BoomerChiao/ArduinoBirthday-Gift-DIY/JPG/3D_STL.jpg

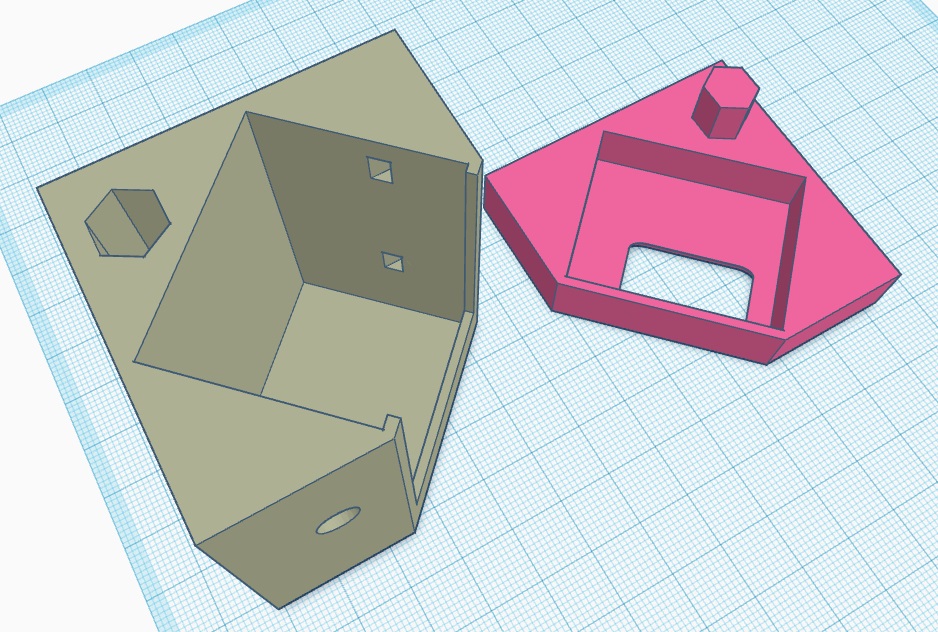
JPG/3D_STL.jpg
