BoomerChiao/ArduinoBirthday-Gift-DIY/JPG/3D_STL_V1.jpg

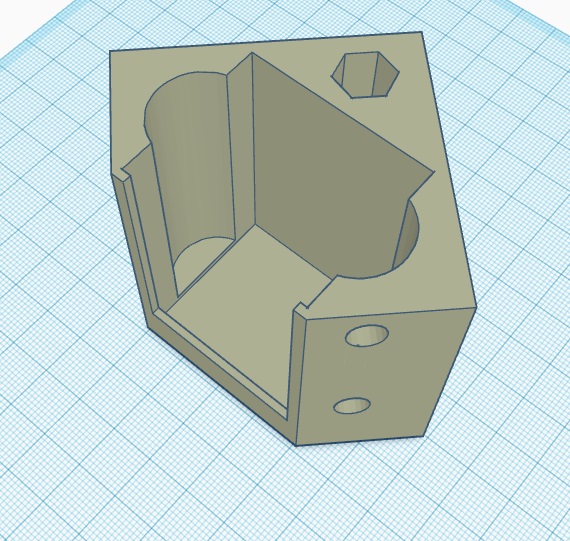
JPG/3D_STL_V1.jpg
