BoomerChiao/ArduinoBirthday-Gift-DIY/JPG/Arduino_pro_mini_LINE.png

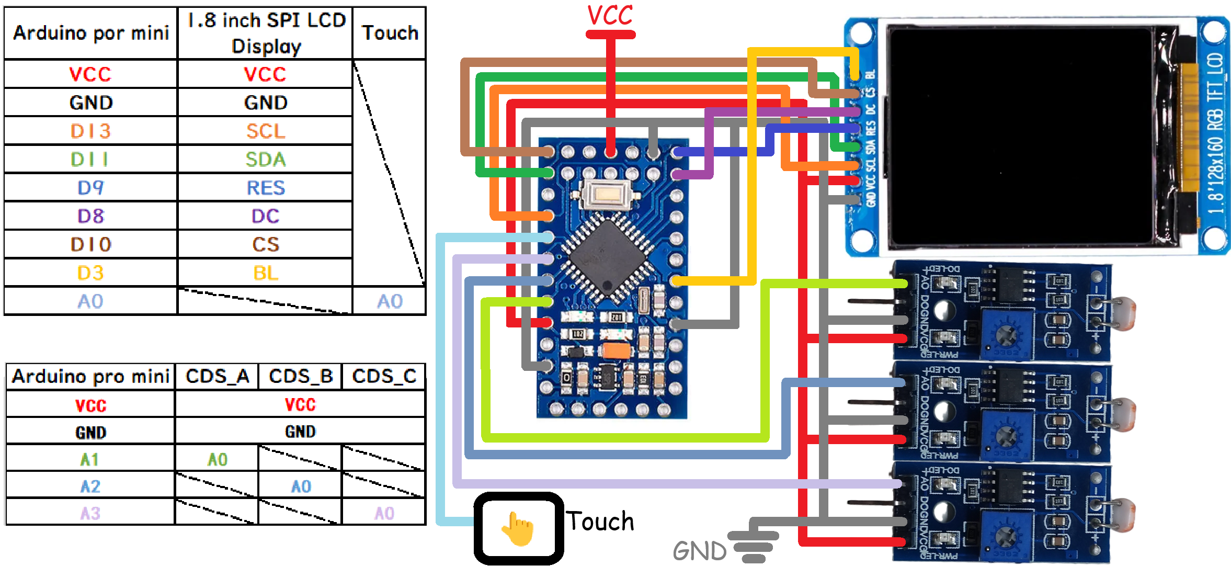
JPG/Arduino_pro_mini_LINE.png
