BoomerChiao/ArduinoBirthday-Gift-DIY/JPG/code.jpg

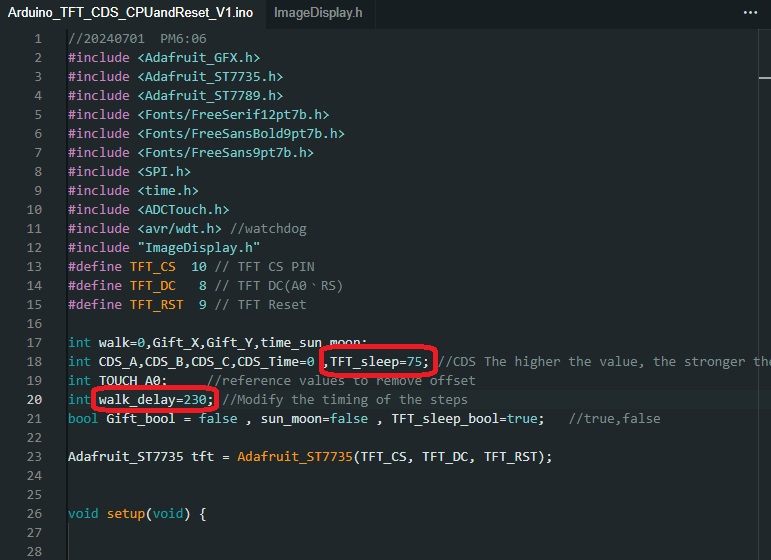
JPG/code.jpg
