BoomerChiao/ArduinoBirthday-Gift-DIY/JPG/IMG_7127.JPG

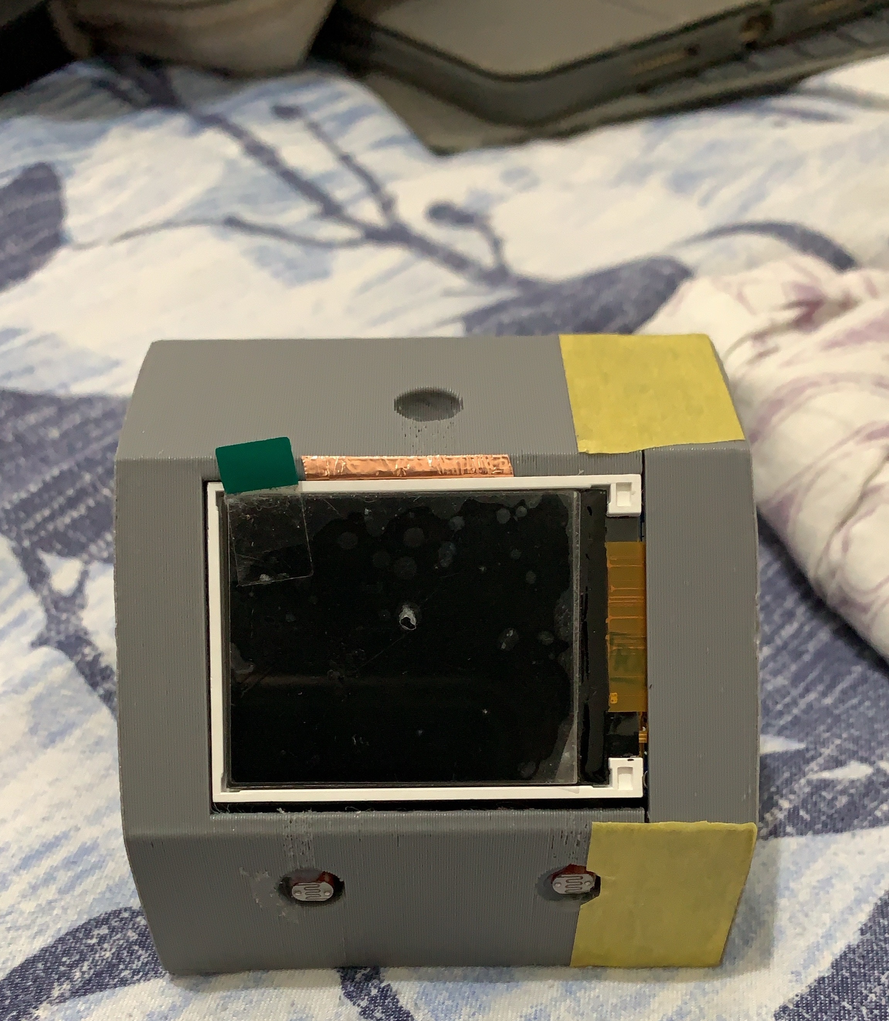
JPG/IMG_7127.JPG
