BoomerChiao/ArduinoBirthday-Gift-DIY/JPG/IMG_7605.jpg

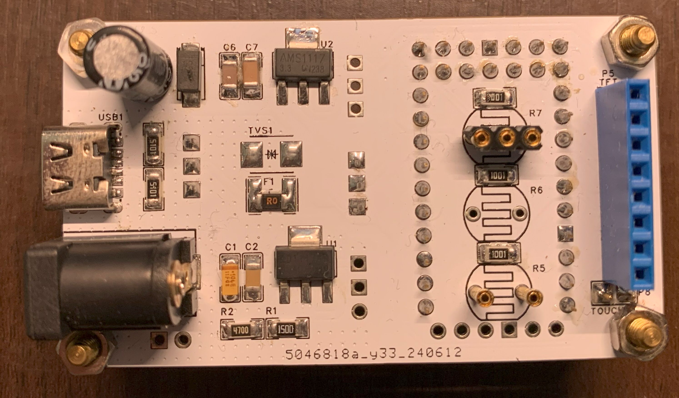
JPG/IMG_7605.jpg
