BoomerChiao/ArduinoBirthday-Gift-DIY/JPG/IMG_7606.jpg

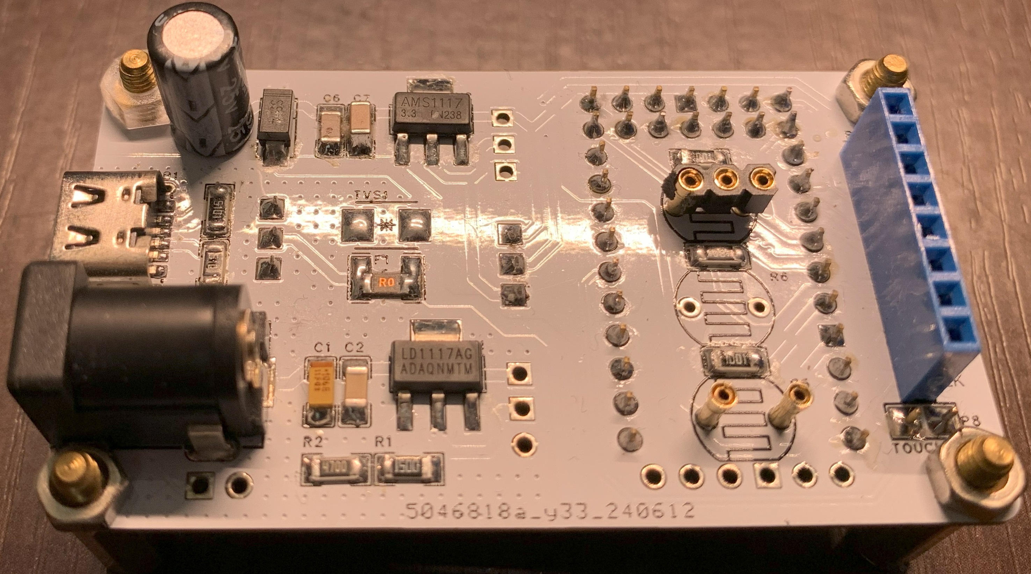
JPG/IMG_7606.jpg
