BoomerChiao/ArduinoBirthday-Gift-DIY/JPG/IMG_7607.jpg

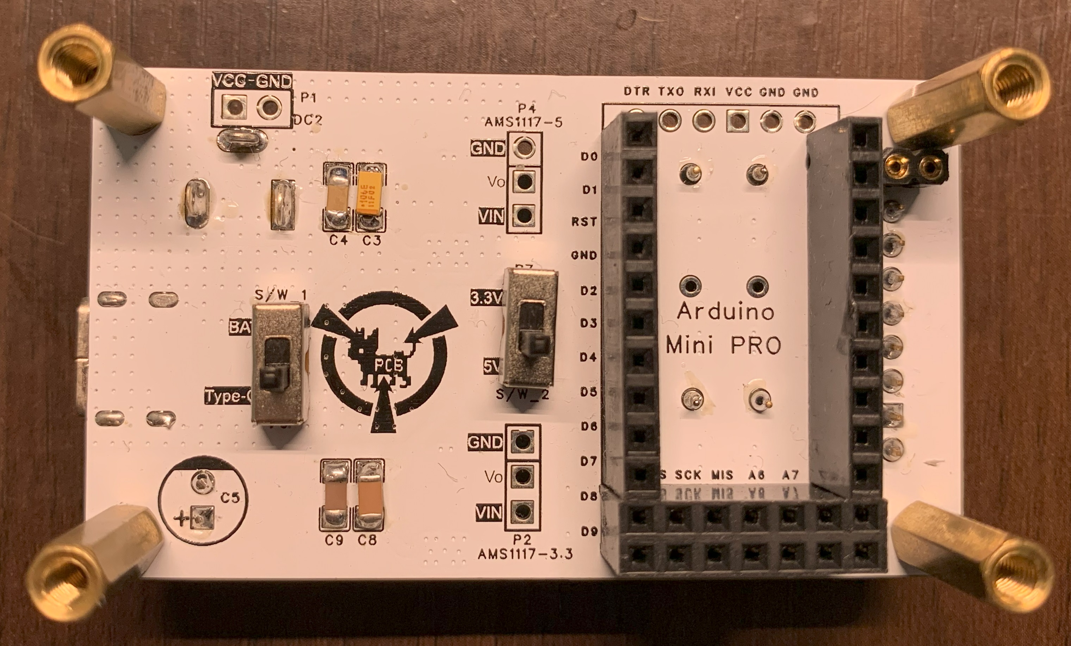
JPG/IMG_7607.jpg
