BoomerChiao/ArduinoBirthday-Gift-DIY/JPG/IMG_7608.jpg

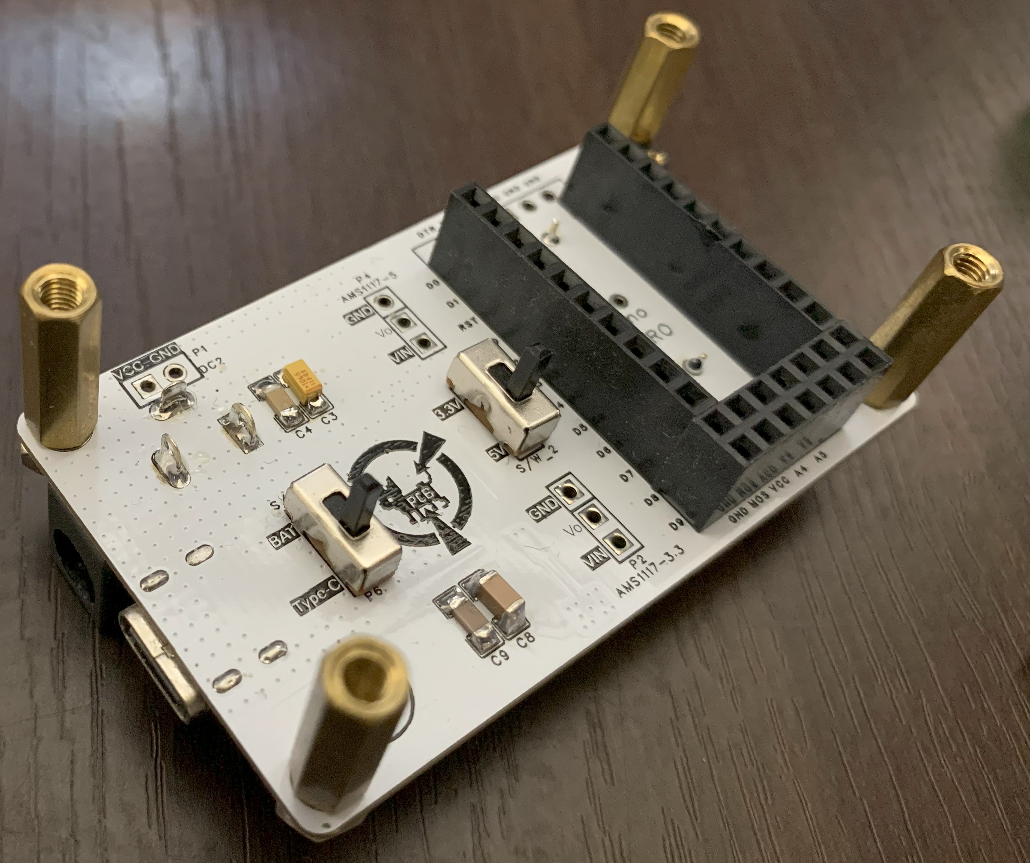
JPG/IMG_7608.jpg
