BoomerChiao/ArduinoBirthday-Gift-DIY/JPG/IMG_7611.jpg

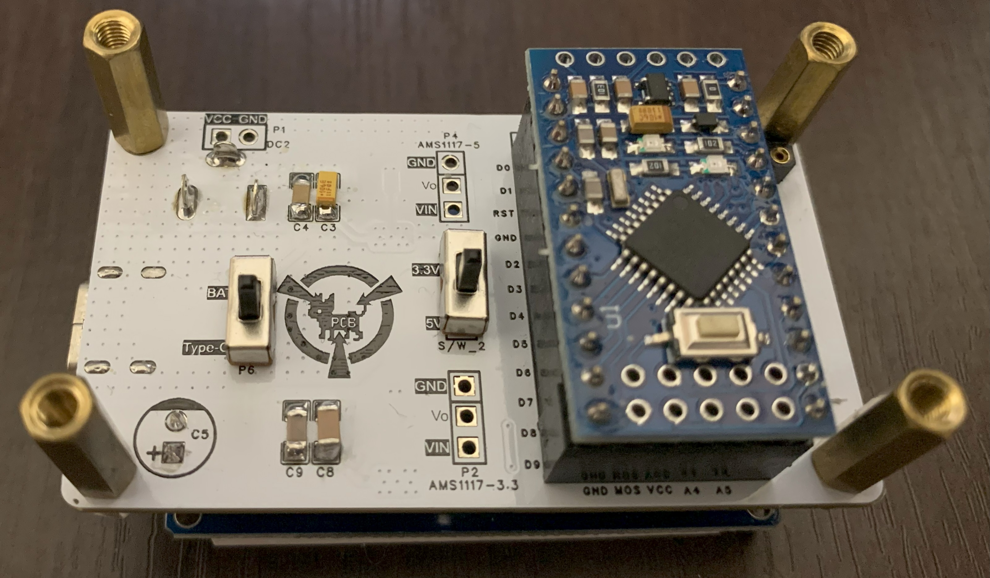
JPG/IMG_7611.jpg
