BoomerChiao/ArduinoBirthday-Gift-DIY/JPG/IMG_7613.jpg

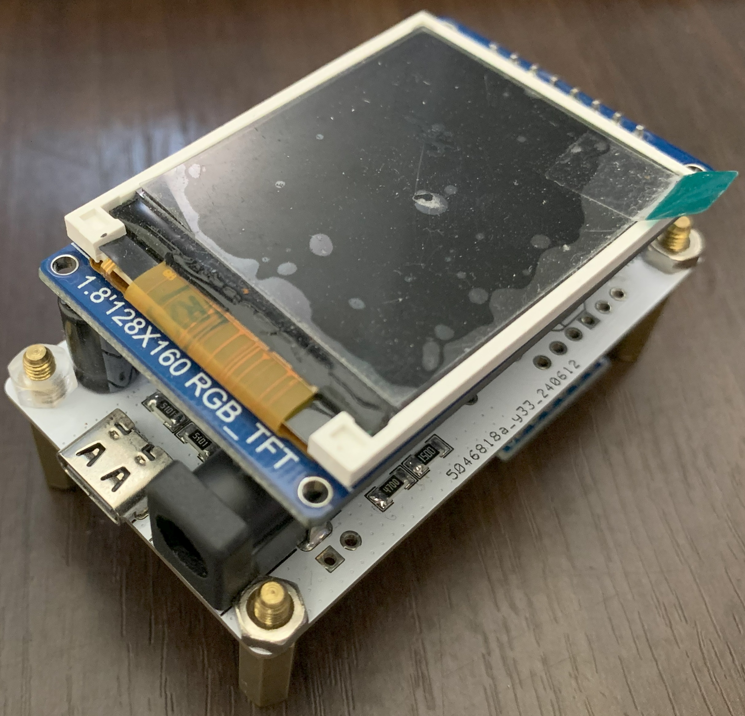
JPG/IMG_7613.jpg
