BoomerChiao/ArduinoBirthday-Gift-DIY/JPG/IMG_7615.jpg

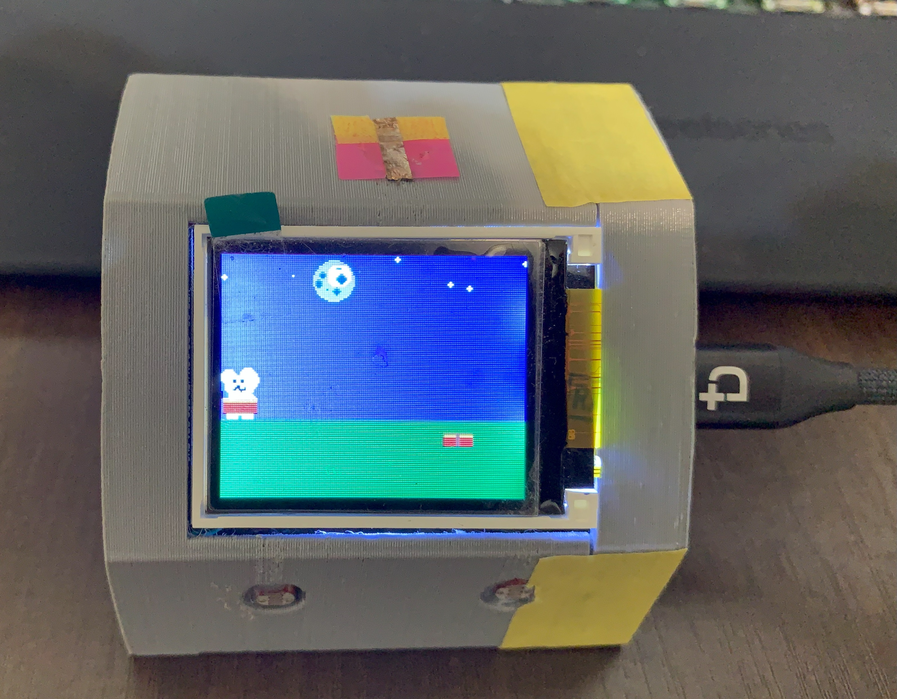
JPG/IMG_7615.jpg
