BoomerChiao/ArduinoBirthday-Gift-DIY/JPG/IMG_7616.jpg

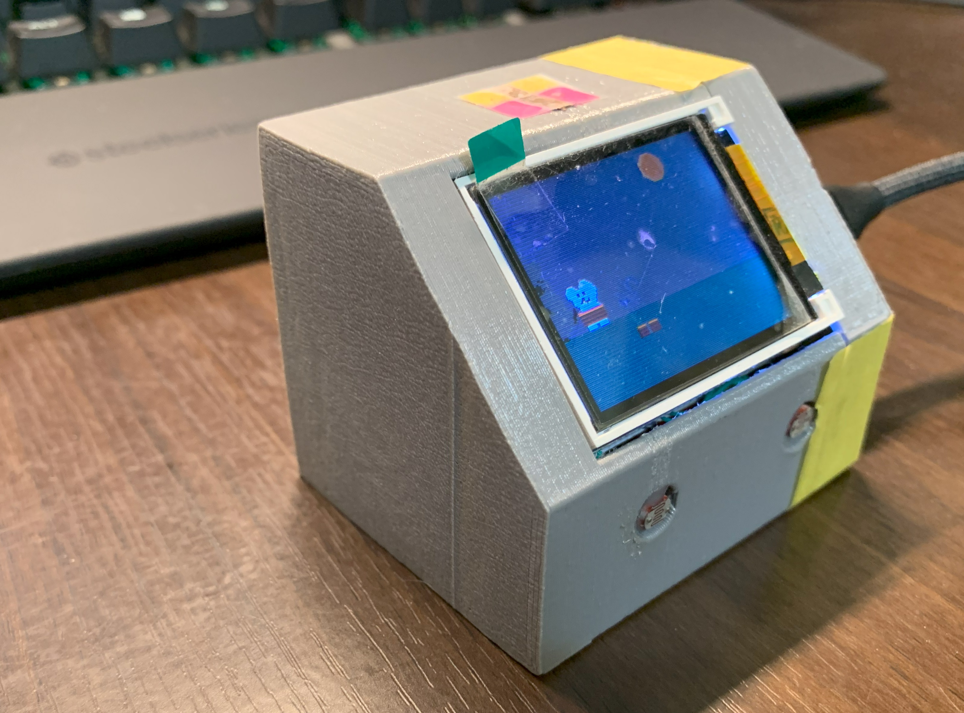
JPG/IMG_7616.jpg
