BoomerChiao/ArduinoBirthday-Gift-DIY/JPG/IMG_7617.jpg

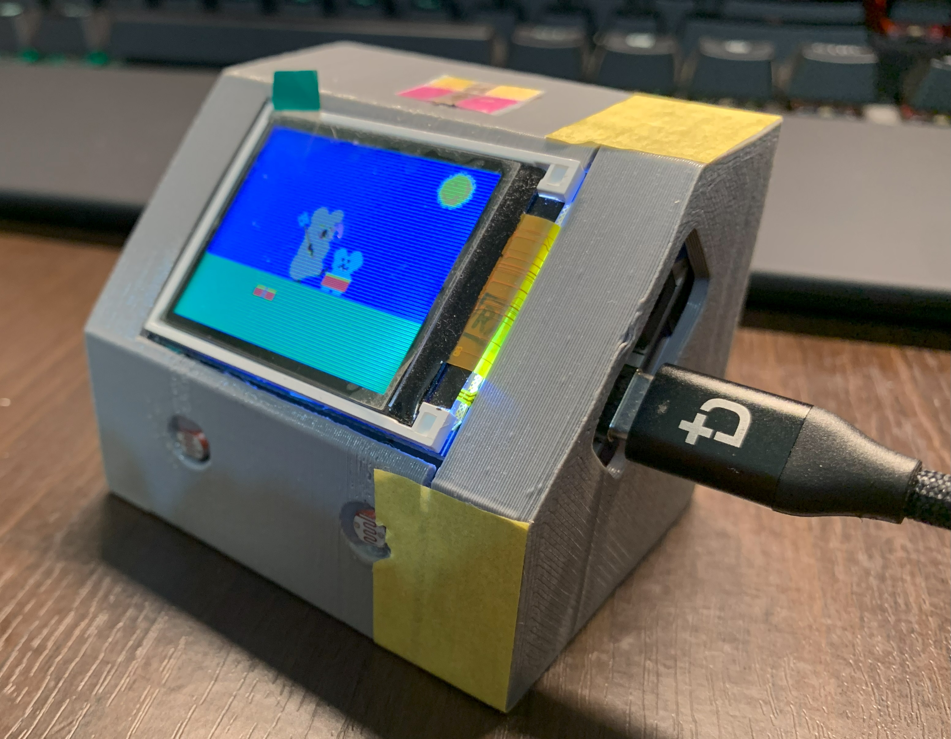
JPG/IMG_7617.jpg
