BoomerChiao/ArduinoBirthday-Gift-DIY/JPG/IMG_7619.jpg

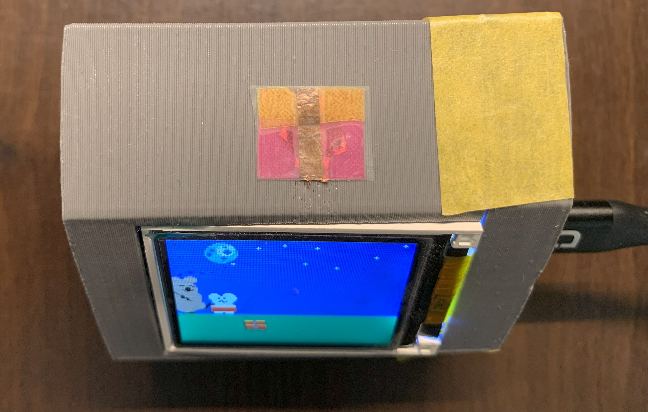
JPG/IMG_7619.jpg
