BoomerChiao/ArduinoBirthday-Gift-DIY/JPG/IMG_7621.jpg

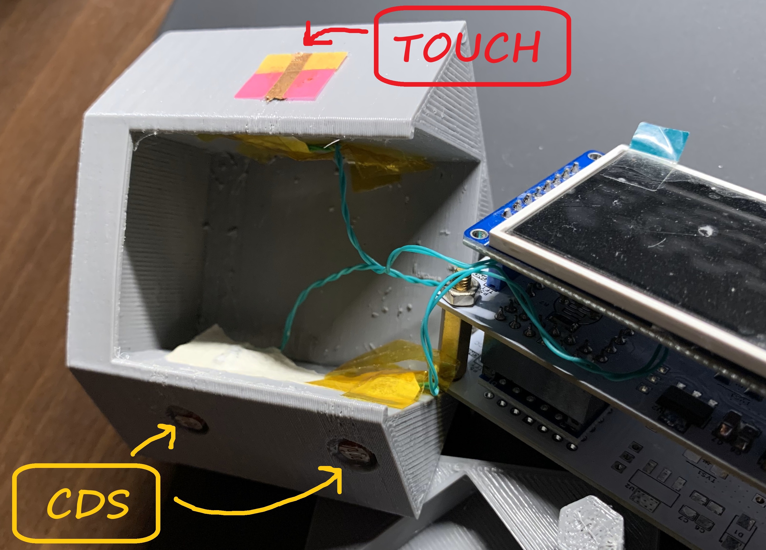
JPG/IMG_7621.jpg
