BoomerChiao/ArduinoBirthday-Gift-DIY/JPG/layout.png

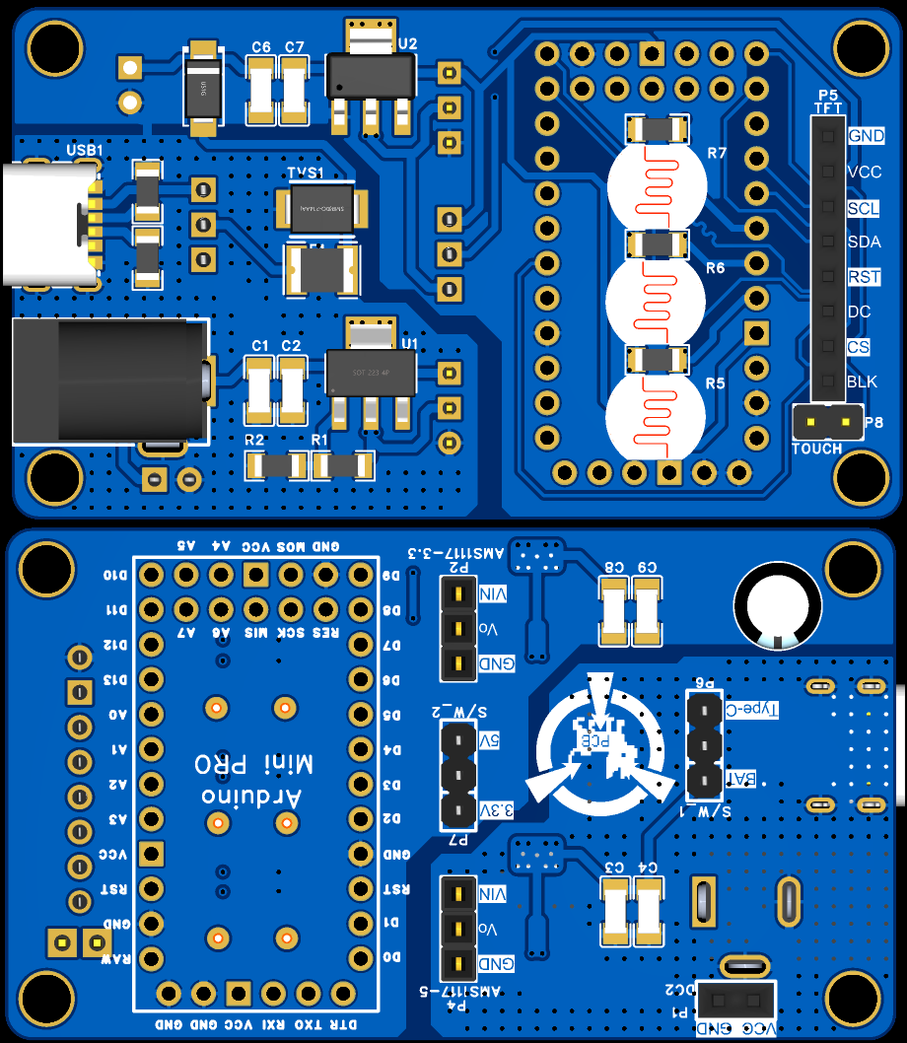
JPG/layout.png
