BoomerChiao/ArduinoBirthday-Gift-DIY/JPG/Lower_Res/IMG_7127.jpg

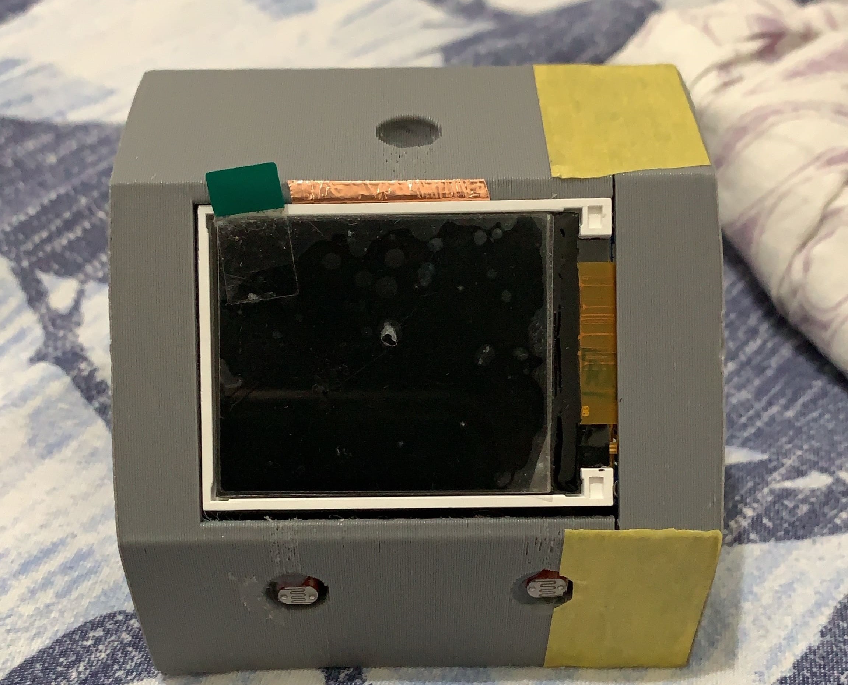
JPG/Lower_Res/IMG_7127.jpg
