BoomerChiao/ArduinoBirthday-Gift-DIY/JPG/Lower_Res/IMG_7615.jpg

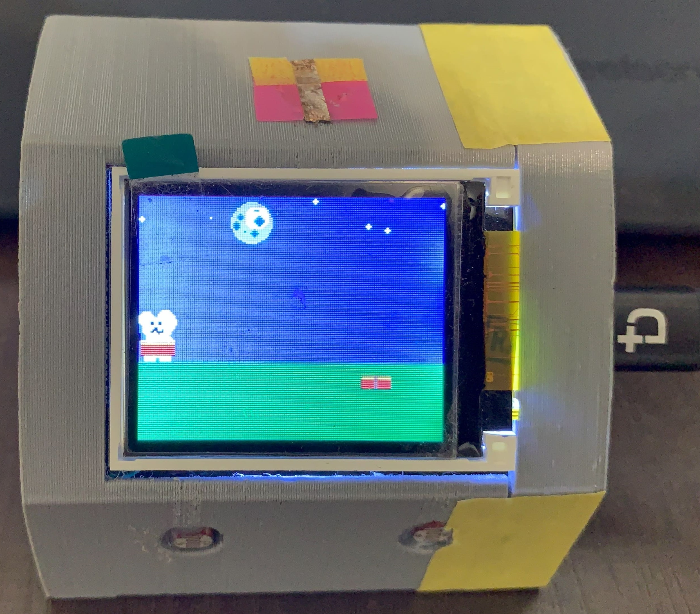
JPG/Lower_Res/IMG_7615.jpg
