BoomerChiao/ArduinoBirthday-Gift-DIY/JPG/Lower_Res/IMG_7616.jpg

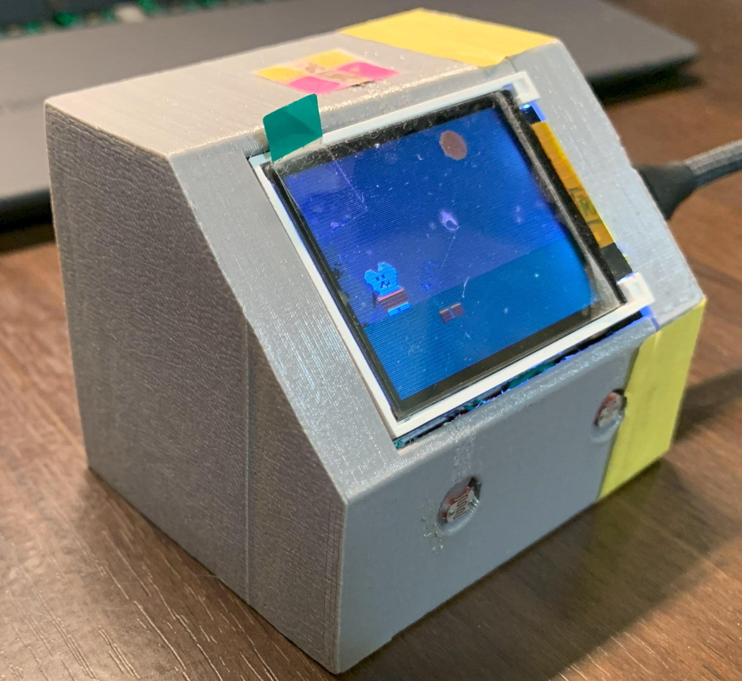
JPG/Lower_Res/IMG_7616.jpg
