BoomerChiao/ArduinoBirthday-Gift-DIY/JPG/Lower_Res/IMG_7617.jpg

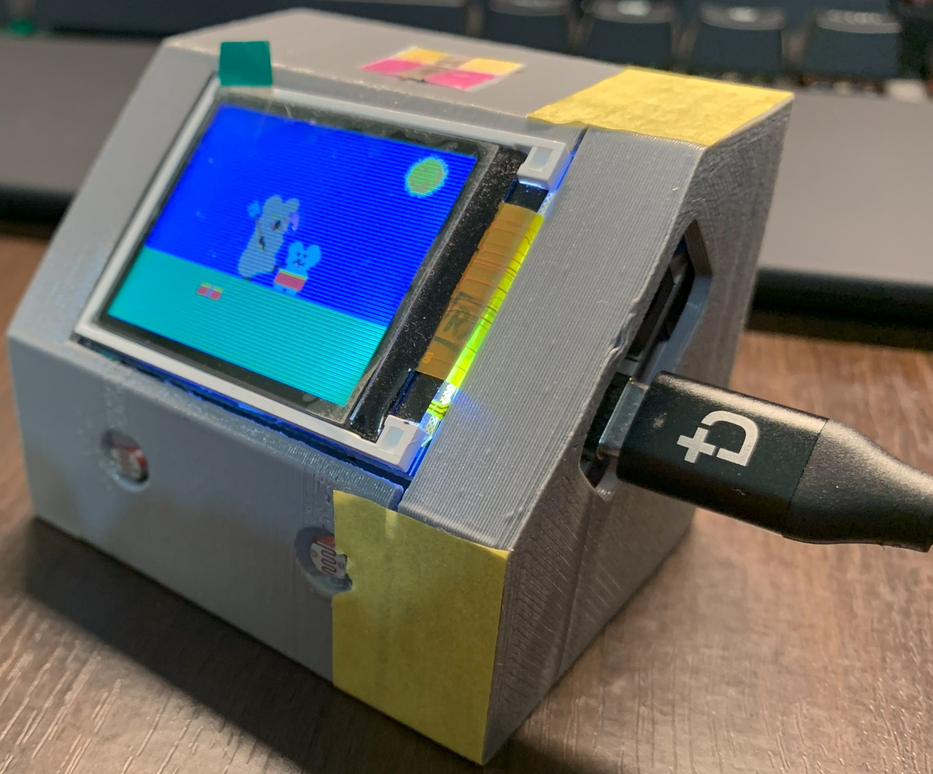
JPG/Lower_Res/IMG_7617.jpg
