BoomerChiao/ArduinoBirthday-Gift-DIY/Code/Arduino_TFT/ImageDisplay.h

const uint16_t CCC[] PROGMEM  = {
0x0000, 0x0000, 0x0000, 0x0000, 0x0000, 0x0000, 0x0000, 0x0000, 0x0000, 0x0000, 0x0000, 0x0000, 0x0000, 0x0000, 0x0000, 0x0000, 0x0000, 0x0000, 0x0000, 0x0000, 0x0000, 0x0000, 0x0000, 0xcc8b, 0xcc8b, 0xcc8b, 0x0000, 0x0000, 0x0000, 0x0000, 0x0000, 0x0000, 0x0000, 0x0000, 0x0000, 0x0000, 
0x0000, 0x0000, 0x0000, 0x0000, 0x0000, 0x0000, 0x0000, 0x0000, 0x0000, 0x0000, 0x0000, 0xcc8b, 0xcc8b, 0xcc8b, 0xcc8b, 0xcc8b, 0x0000, 0x0000, 0x0000, 0x0000, 0x0000, 0xcc8b, 0xcc8b, 0xcc8b, 0xcc8b, 0xcc8b, 0xcc8b, 0xcc8b, 0x0000, 0x0000, 0x0000, 0x0000, 0x0000, 0x0000, 0x0000, 0x0000, 
0x0000, 0x0000, 0x0000, 0x0000, 0x0000, 0x0000, 0x0000, 0x0000, 0x0000, 0x0000, 0xcc8b, 0xcc8b, 0xcc8b, 0xcc8b, 0xcc8b, 0xcc8b, 0xcc8b, 0x0000, 0x0000, 0x0000, 0xcc8b, 0xcc8b, 0xcc8b, 0xcc8b, 0xcc8b, 0xcc8b, 0xcc8b, 0xcc8b, 0xcc8b, 0x0000, 0x0000, 0x0000, 0x0000, 0x0000, 0x0000, 0x0000, 
0x0000, 0x0000, 0x0000, 0x0000, 0x0000, 0x0000, 0x0000, 0x0000, 0x0000, 0xcc8b, 0xcc8b, 0xcc8b, 0xcc8b, 0xcc8b, 0xcc8b, 0xcc8b, 0xcc8b, 0xcc8b, 0x0000, 0x0000, 0xcc8b, 0xcc8b, 0xcc8b, 0xcc8b, 0xcc8b, 0xcc8b, 0xcc8b, 0xcc8b, 0xcc8b, 0x0000, 0x0000, 0x0000, 0x0000, 0x0000, 0x0000, 0x0000, 
0x0000, 0x0000, 0x0000, 0x0000, 0x0000, 0x0000, 0x0000, 0x0000, 0xcc8b, 0xcc8b, 0xcc8b, 0xcc8b, 0xcc8b, 0xcc8b, 0xcc8b, 0xcc8b, 0xcc8b, 0xcc8b, 0xcc8b, 0xcc8b, 0xcc8b, 0xcc8b, 0xcc8b, 0xcc8b, 0xcc8b, 0xcc8b, 0xcc8b, 0xcc8b, 0xcc8b, 0x0000, 0x0000, 0x0000, 0x0000, 0x0000, 0x0000, 0x0000, 
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
0x6358, 0x6358, 0x6358, 0x6358, 0x6358, 0x6358, 0x6358, 0x6358, 0xef36, 0xef36, 0xef36, 0xef36, 0xef36, 0xef36, 0x6358, 0x6358, 0x6358, 0x6358, 0x6358, 0x6358, 0x6358, 0x6358
  };
